alexose/dorothy/images/1.jpeg

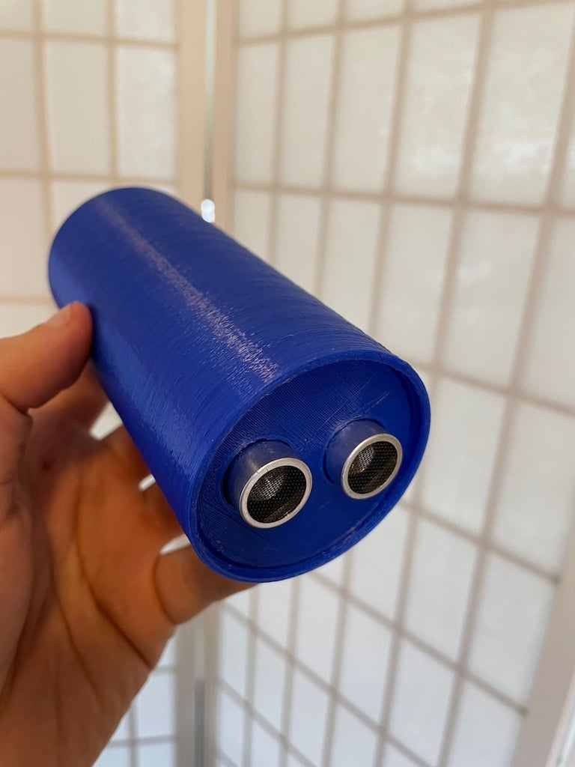
images/1.jpeg
