alexose/dorothy/images/2.jpeg

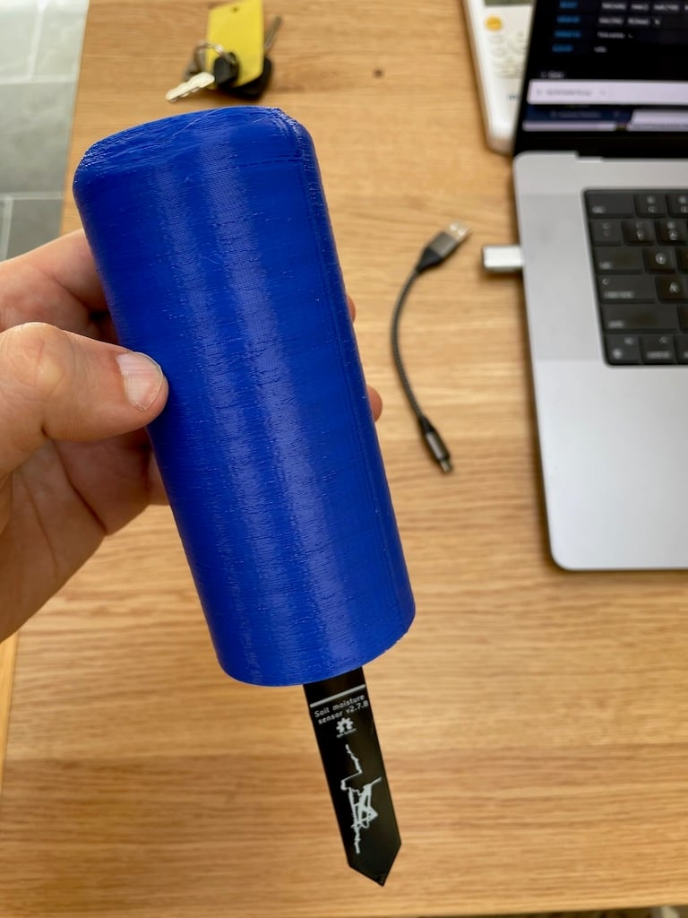
images/2.jpeg
