alexose/dorothy/images/3.jpeg

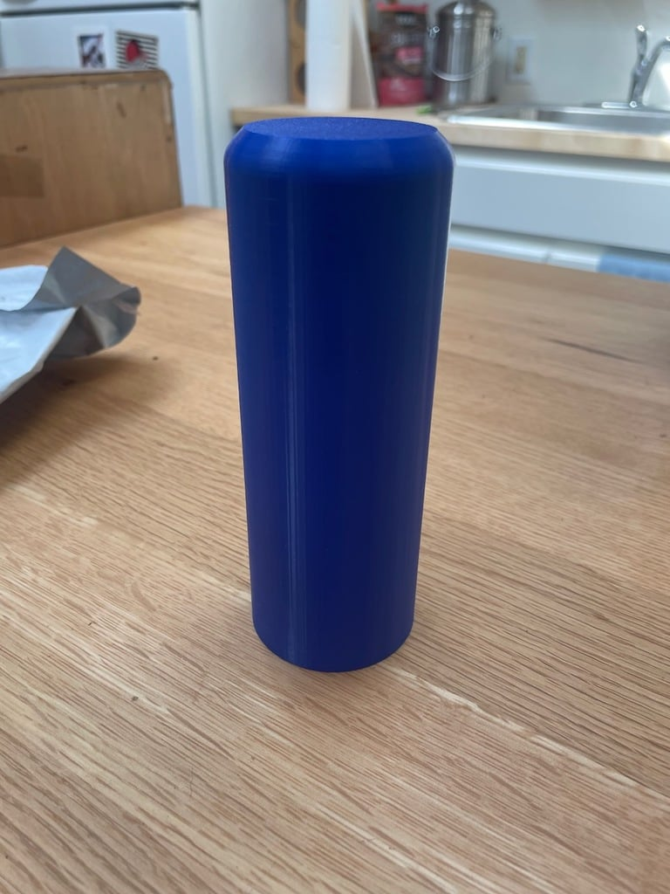
images/3.jpeg
