alexose/dorothy/images/4.jpeg

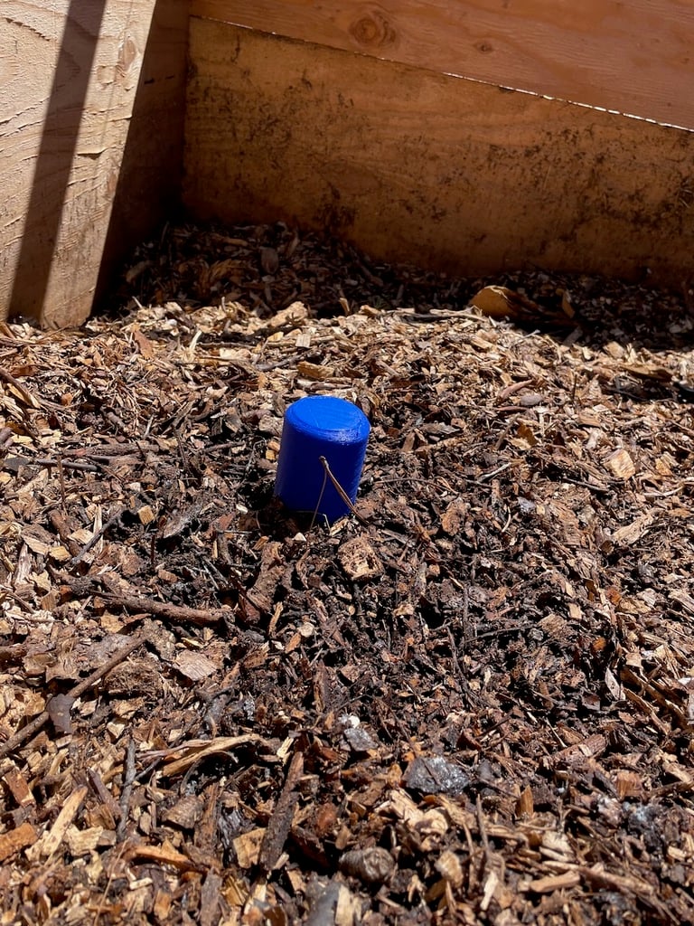
images/4.jpeg
