alexose/dorothy/images/5.jpeg

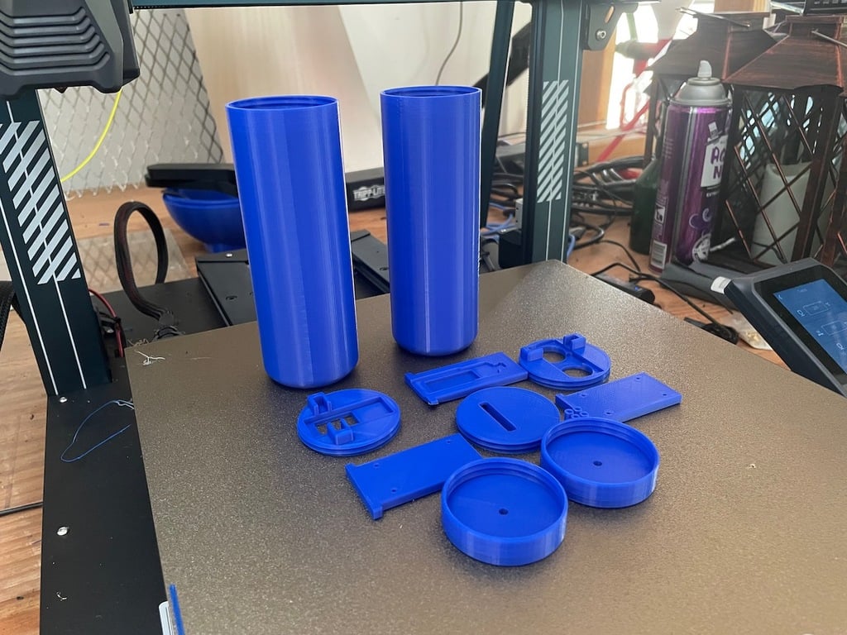
images/5.jpeg
