alexose/dorothy/images/6.jpeg

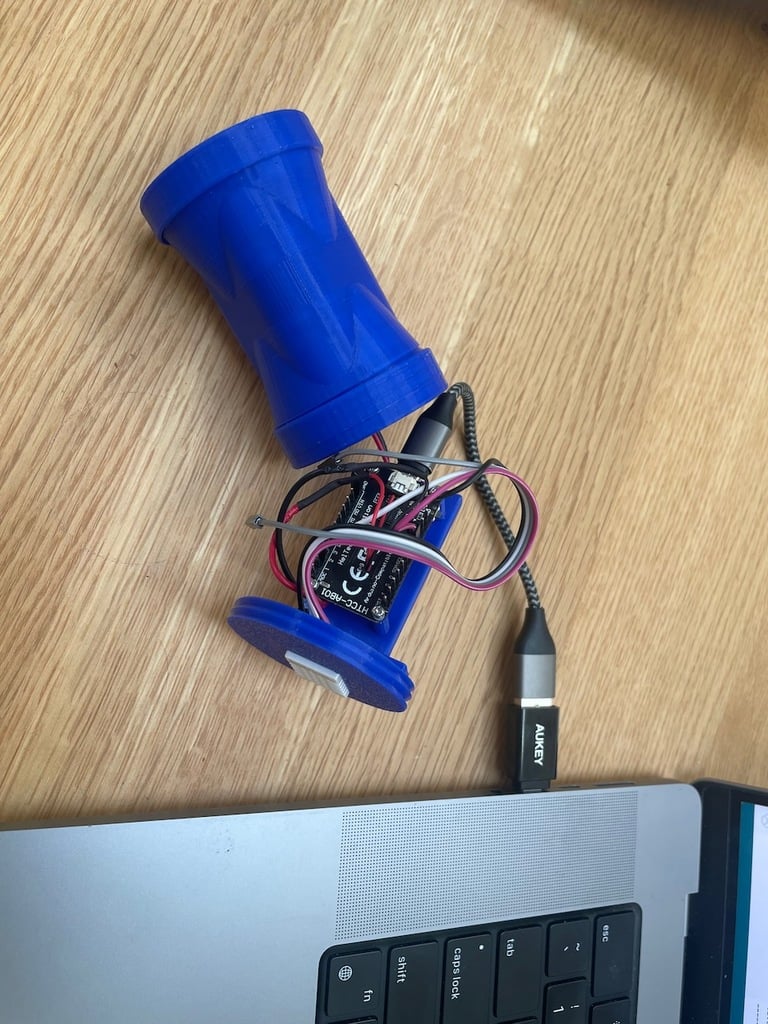
images/6.jpeg
