alexose/dorothy/images/7.jpeg

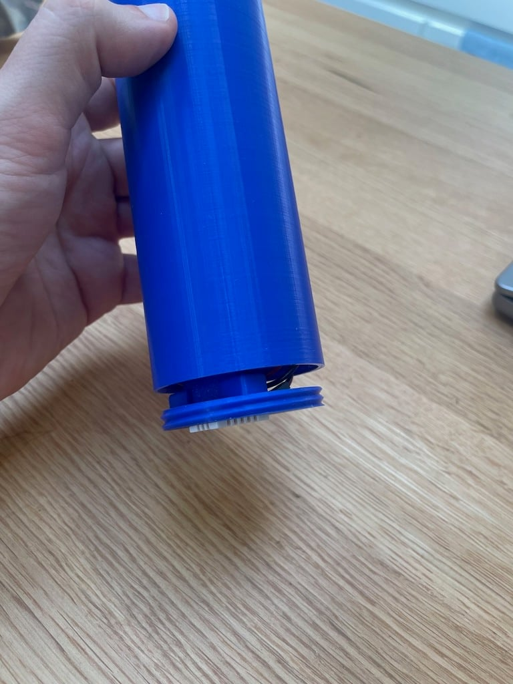
images/7.jpeg
