alexose/dorothy/images/8.jpeg

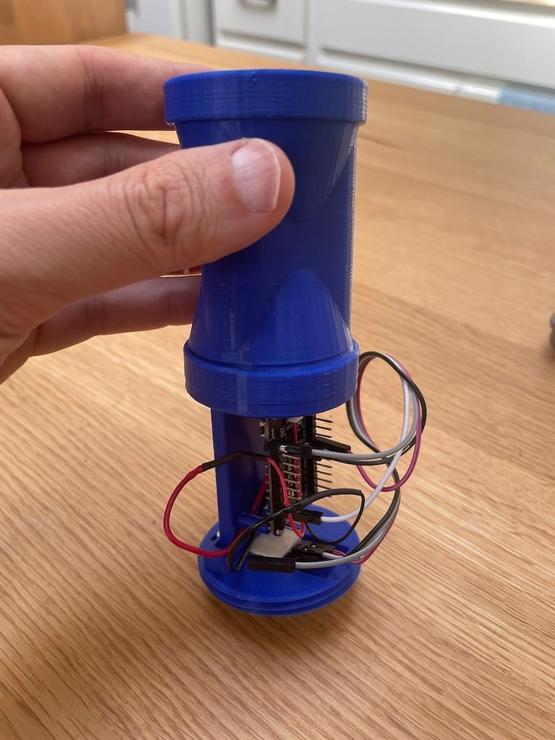
images/8.jpeg
